sparkfun/SparkFun_RTK_Postcard/docs/assets/img/README.md

img directory
====================
This folder should contain the images for the product documentation

## General Images
- `sfe-logo.png` - SparkFun flame logo (favicon)

## Directory
- `graphical_datasheet` - Files for graphical datasheet
- `hookup_guide` - Images for the hookup guide pages
- `qr_code` - QR code images
- `qwiic` - Images for Qwiic Banner

## QR Codes
- [QR code generator](https://qrgenerator.org/)
	- Flame Color: #E0311D
	- Frame Color: #3C464D
- [Remove meta data from svg](https://jakearchibald.github.io/svgomg/)
