sparkfun/SparkFun_RTK_Postcard/docs/assets/board_files/dimensions.pdf

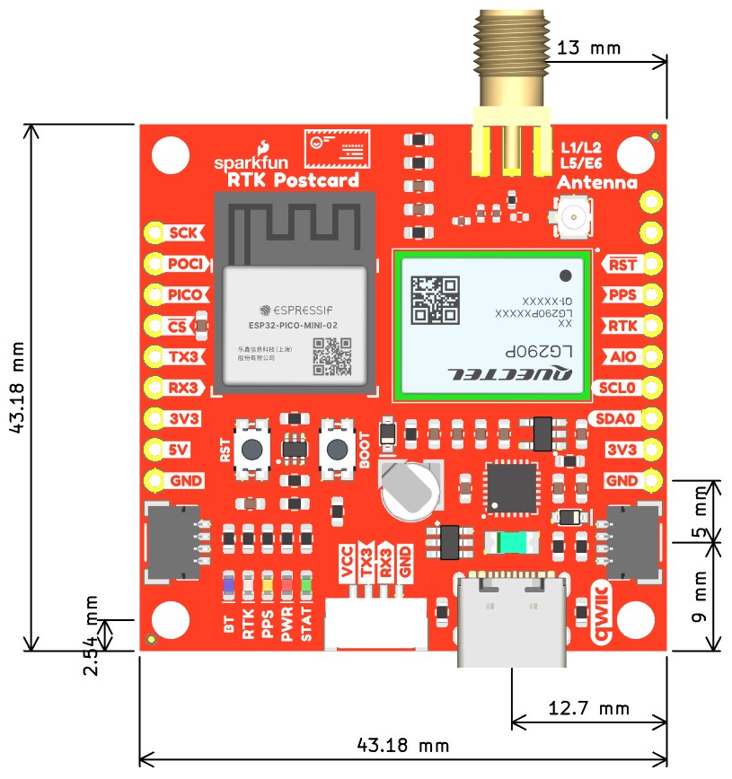
[picture p49: page 1]
