sparkfun/SparkFun_RTK_Postcard/docs/assets/3d_model/enclosure/poster.png

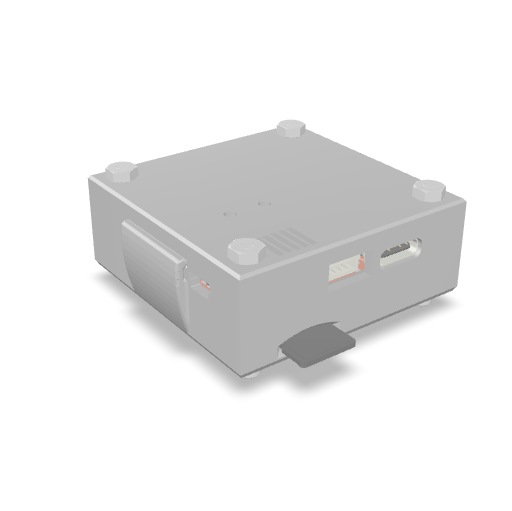
docs/assets/3d_model/enclosure/poster.png
