sparkfun/SparkFun_RTK_Postcard/docs/assets/3d_model/poster.png

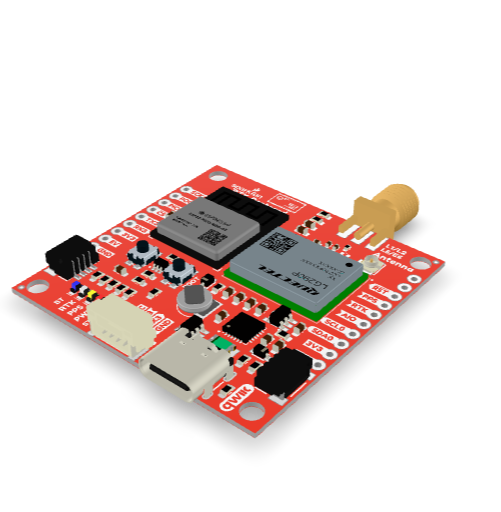
docs/assets/3d_model/poster.png
