sparkfun/SparkFun_RTK_Postcard/docs/assets/img/hookup_guide/specs-antenna.png

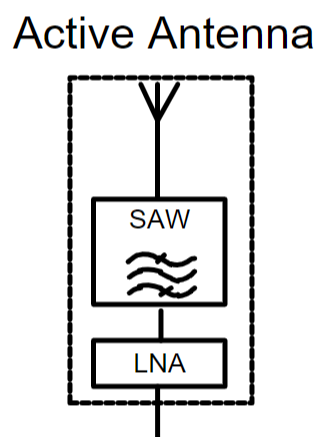
docs/assets/img/hookup_guide/specs-antenna.png
