sparkfun/SparkFun_RTK_Postcard/docs/assets/img/thumbnail.jpg

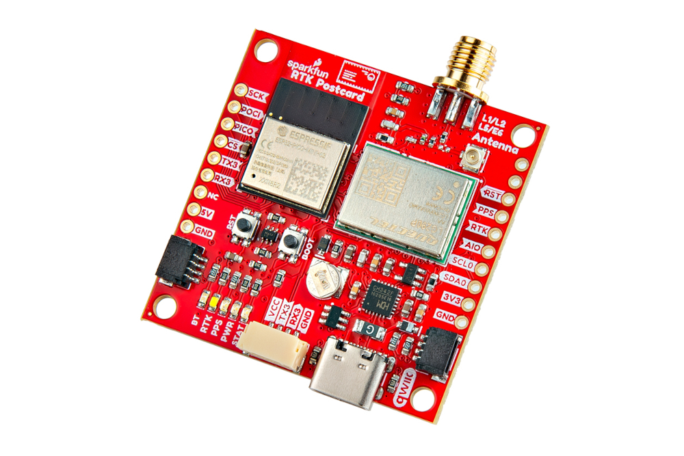
docs/assets/img/thumbnail.jpg
