sparkfun/SparkFun_RTK_Postcard/docs/assets/img/hookup_guide/antenna_modification.png

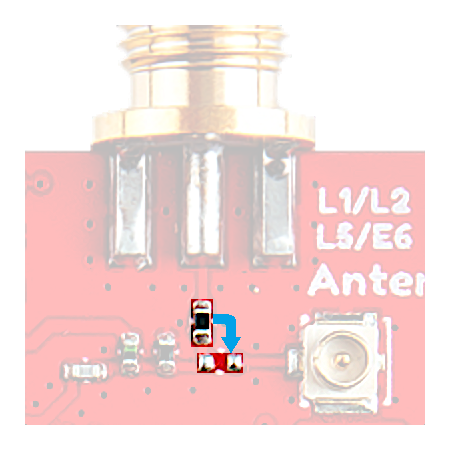
docs/assets/img/hookup_guide/antenna_modification.png
