sparkfun/SparkFun_RTK_Postcard/docs/assets/img/hookup_guide/assembly-antenna_modification.jpg

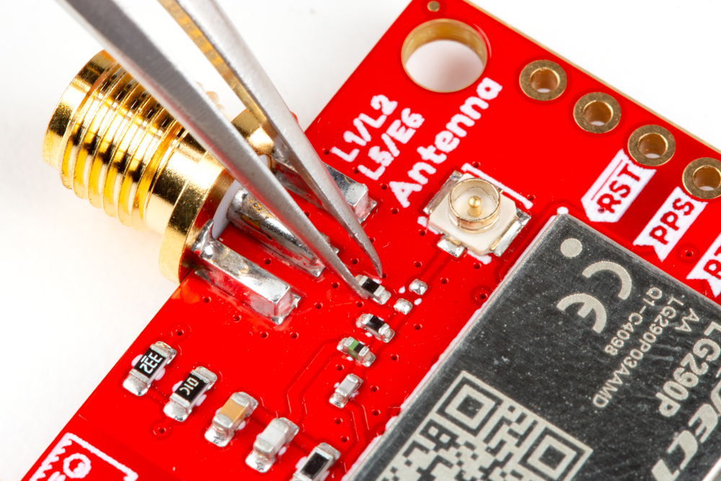
docs/assets/img/hookup_guide/assembly-antenna_modification.jpg
