sparkfun/SparkFun_RTK_Postcard/docs/assets/img/hookup_guide/assembly-bluetooth_setup.jpg

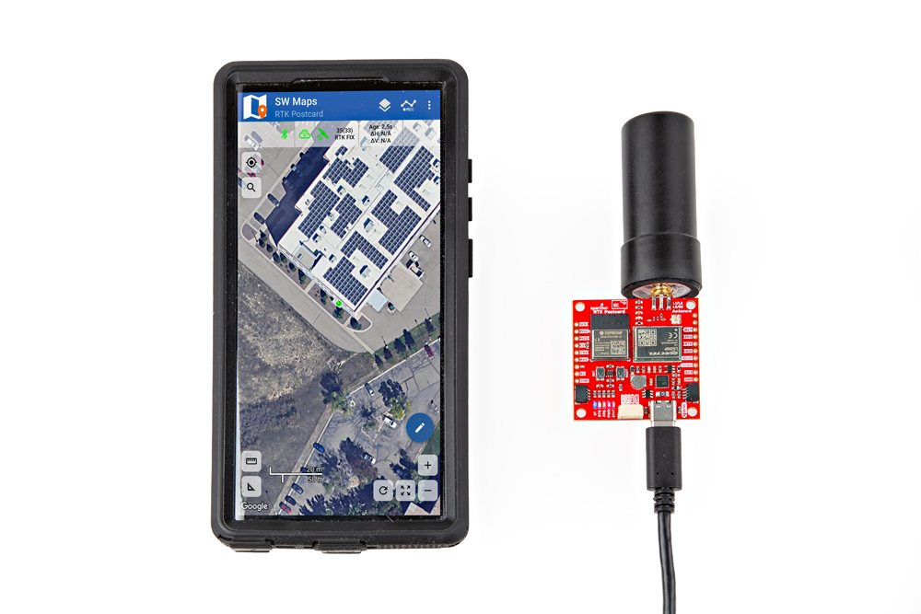
docs/assets/img/hookup_guide/assembly-bluetooth_setup.jpg
