sparkfun/SparkFun_RTK_Postcard/docs/assets/img/hookup_guide/assembly-header_modification.jpg

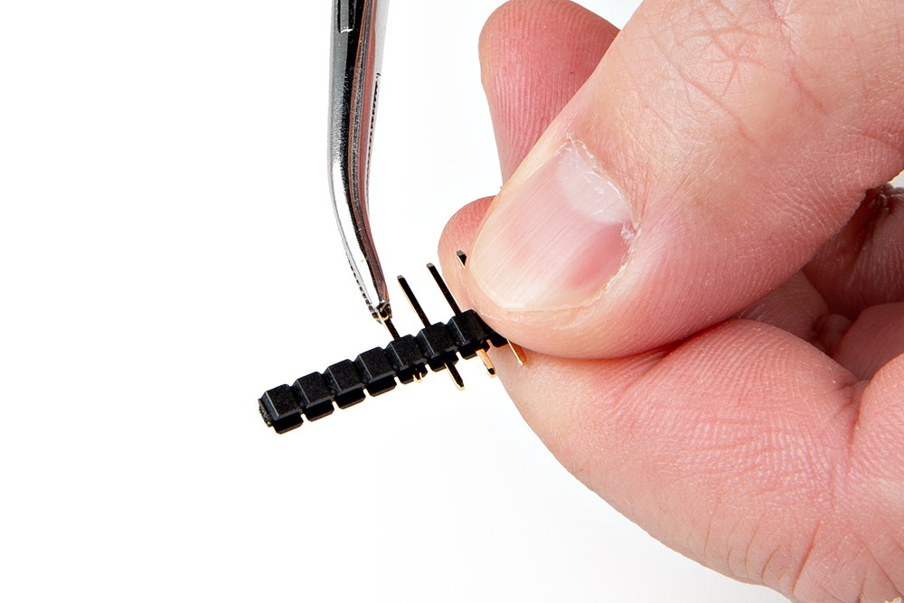
docs/assets/img/hookup_guide/assembly-header_modification.jpg
