sparkfun/SparkFun_RTK_Postcard/docs/assets/img/hookup_guide/assembly-portability_shield-battery-1300mah2.jpg

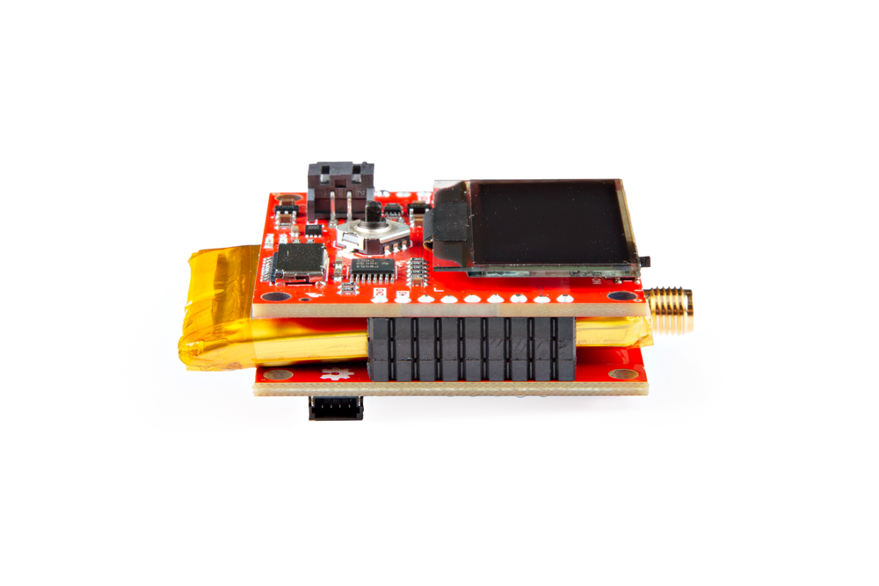
docs/assets/img/hookup_guide/assembly-portability_shield-battery-1300mah2.jpg
