sparkfun/SparkFun_RTK_Postcard/docs/assets/img/hookup_guide/assembly-portability_shield.jpg

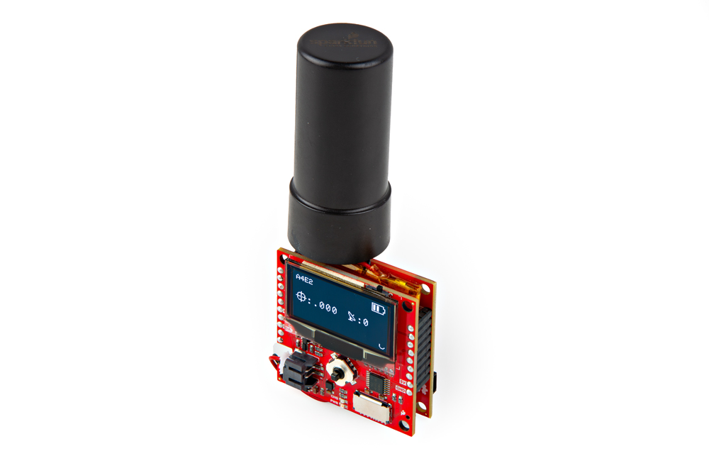
docs/assets/img/hookup_guide/assembly-portability_shield.jpg
