sparkfun/SparkFun_RTK_Postcard/docs/assets/img/hookup_guide/assembly-qwiic_peripheral.jpg

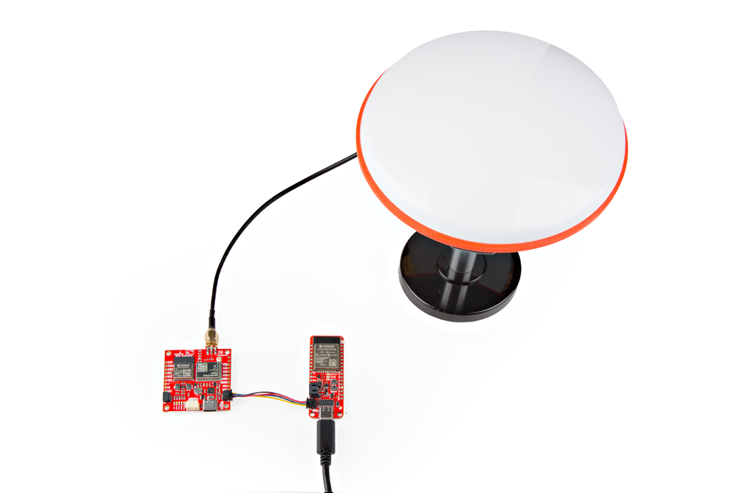
docs/assets/img/hookup_guide/assembly-qwiic_peripheral.jpg
