sparkfun/SparkFun_RTK_Postcard/docs/assets/img/hookup_guide/bottom-original.png

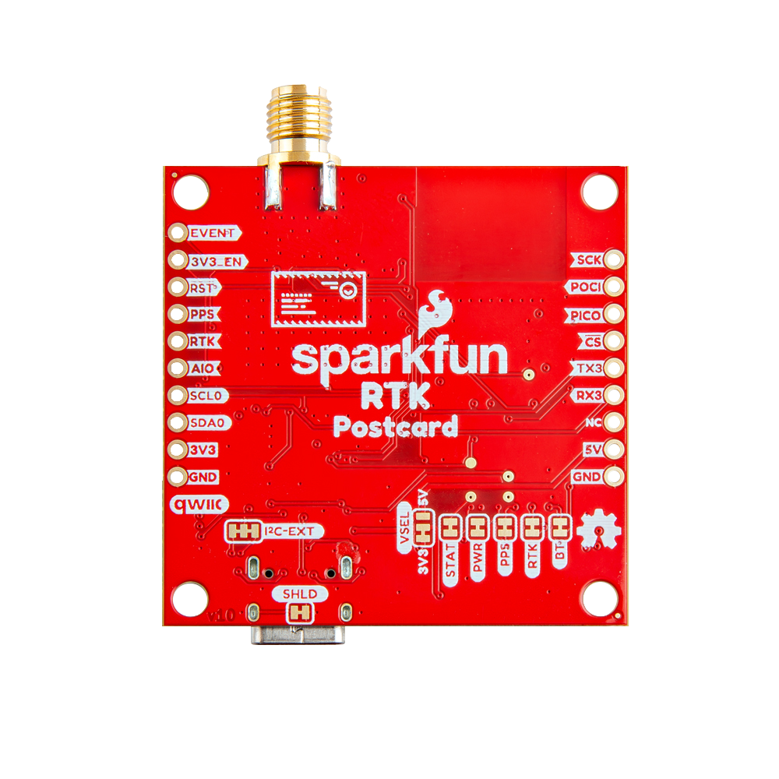
docs/assets/img/hookup_guide/bottom-original.png
