sparkfun/SparkFun_RTK_Postcard/docs/assets/img/hookup_guide/esp32-peripherals2.png

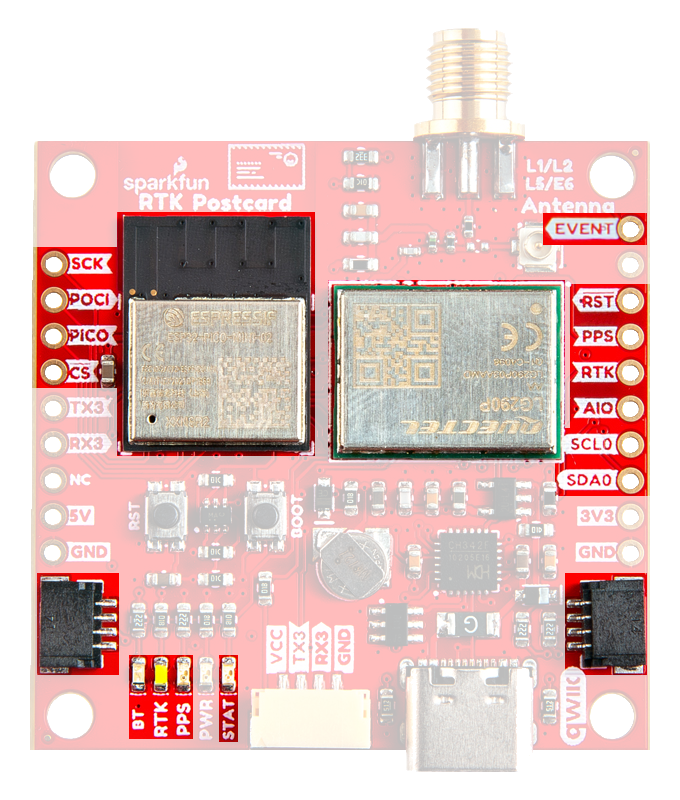
docs/assets/img/hookup_guide/esp32-peripherals2.png
