sparkfun/SparkFun_RTK_Postcard/docs/assets/img/hookup_guide/qgnss-update_firmware.png

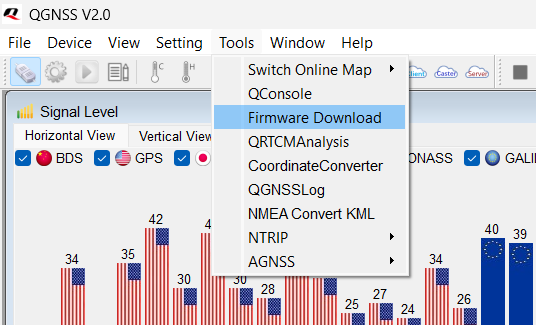
docs/assets/img/hookup_guide/qgnss-update_firmware.png
