sparkfun/SparkFun_RTK_Postcard/docs/assets/img/hookup_guide/top-original.png

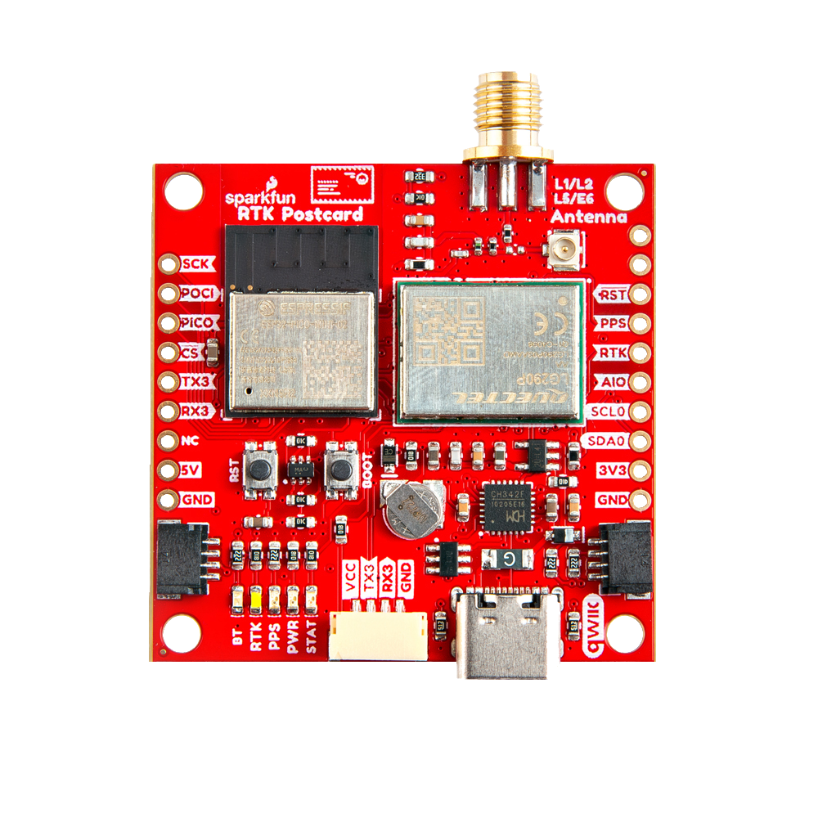
docs/assets/img/hookup_guide/top-original.png
